devindi99/PIR-Sensor-Module/enclosure/THT LED brown.SLDPRT

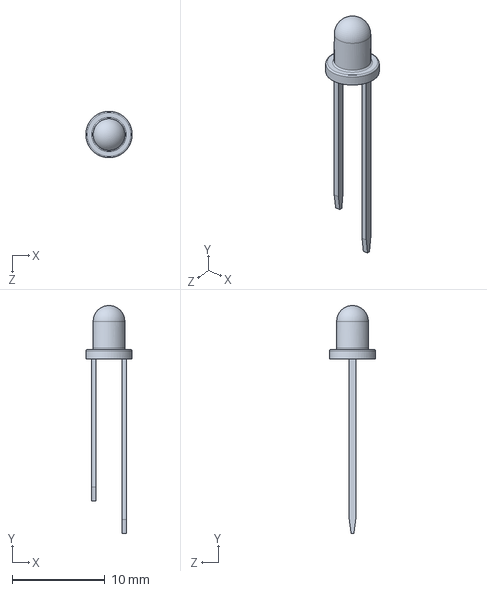
[picture p48: CAD file, 2022-11-16]
enclosure/THT LED brown.SLDPRT
5.00 x 24.5 x 5.00 mm
