devindi99/PIR-Sensor-Module/enclosure/PCB_of_Schematic.step

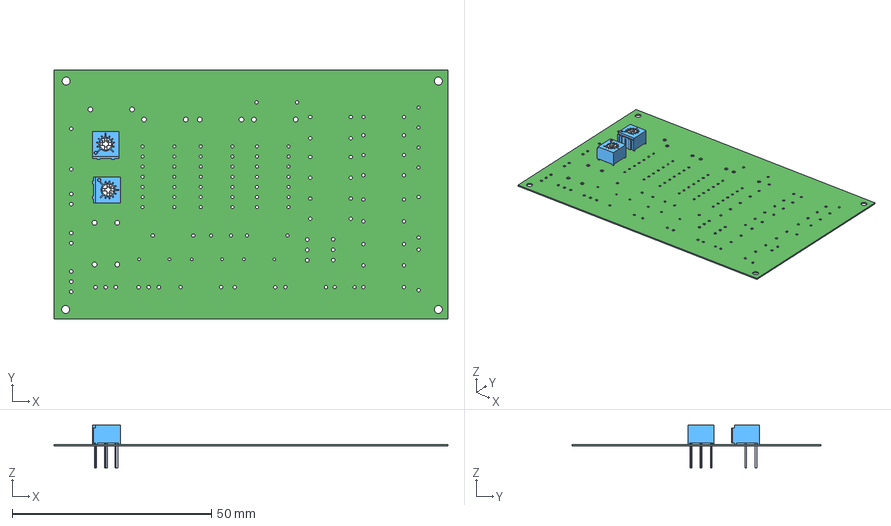
[picture p49: CAD file, 2022-11-16]
enclosure/PCB_of_Schematic.step
98.8 x 62.5 x 10.7 mm
