devindi99/PIR-Sensor-Module/enclosure/SW338-ND.SLDPRT

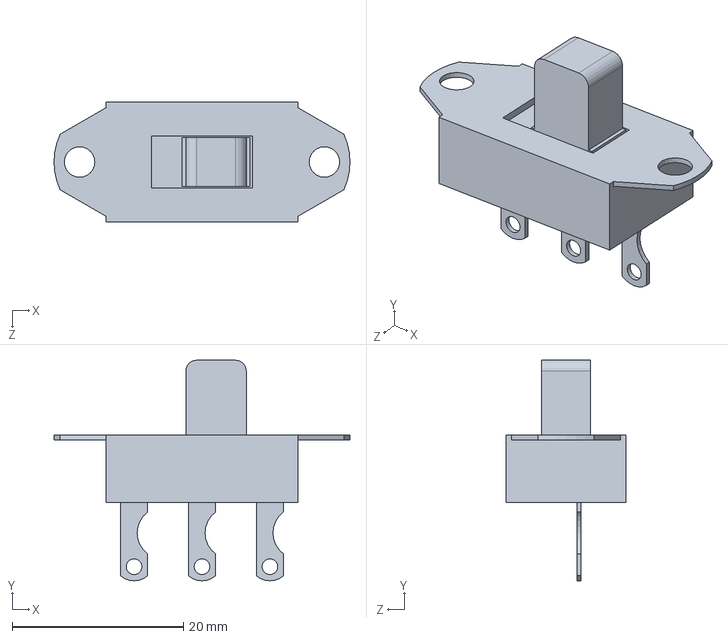
[picture p50: CAD file, 2022-11-16]
enclosure/SW338-ND.SLDPRT
34.5 x 25.8 x 14.0 mm
