devindi99/PIR-Sensor-Module/enclosure/ldr.SLDPRT

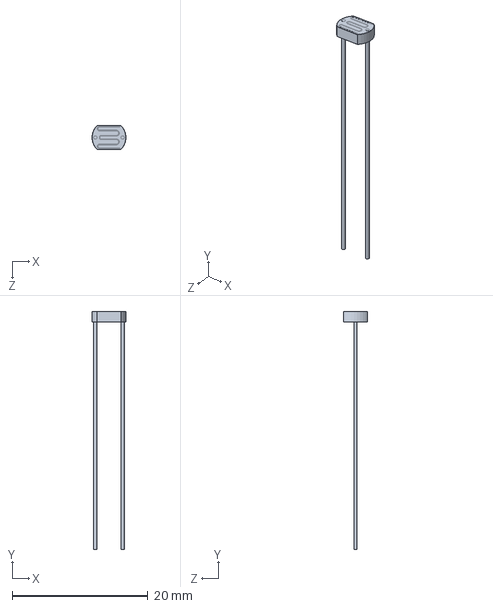
[picture p51: CAD file, 2022-11-16]
enclosure/ldr.SLDPRT
4.98 x 35.0 x 3.60 mm
